nseidle/SwitchBoard-MP3/Firmware/Switchboard_MP3_Player/Transforms.ino

//This is the hardcoded transform of LEDs. It's faster just to manually set it.
//Decoder ring between the I/O board port # and the physical LED location.
//If ledTransform[3] = 17, then the LED location 3 connects with I/O port 17.
void loadRealityArrayLEDs()
{
  ledTransform[60] = 1; //ledTransform[60] = 1, then the LED location 60 connects with I/O port 1 of board B.
  ledTransform[59] = 2;
  ledTransform[58] = 3;
  ledTransform[57] = 4;
  ledTransform[56] = 5;
  ledTransform[55] = 6;
  ledTransform[54] = 7;
  ledTransform[53] = 8;
  ledTransform[52] = 9;
  ledTransform[51] = 10;

  ledTransform[50] = 41; //ledTransform[50] = 41, then the LED location 50 connects with I/O port 1 of board A.
  ledTransform[49] = 42;
  ledTransform[48] = 43;
  ledTransform[47] = 44;
  ledTransform[46] = 45;
  ledTransform[45] = 46;
  ledTransform[44] = 47;
  ledTransform[43] = 48;
  ledTransform[42] = 49;
  ledTransform[41] = 50;

  ledTransform[40] = 11; //ledTransform[40] = 11, then the LED location 40 connects with I/O port 11 of board B.
  ledTransform[39] = 12;
  ledTransform[38] = 13;
  ledTransform[37] = 14;
  ledTransform[36] = 15;
  ledTransform[35] = 16;
  ledTransform[34] = 17;
  ledTransform[33] = 19; //Swap
  ledTransform[32] = 18; //Swap
  ledTransform[31] = 20;

  ledTransform[30] = 51; //ledTransform[30] = 51, then the LED location 30 connects with I/O port 51 of board A.
  ledTransform[29] = 52;
  ledTransform[28] = 53;
  ledTransform[27] = 54;
  ledTransform[26] = 55;
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
  switchTransform[3] = 68; //Repaired 
  switchTransform[2] = 69;
  switchTransform[1] = 70; //switchTransform[1] = 70, then the switch in location 1 connects with input port 70 of board A.  
}
